pmackle/EE-Emerge-2020-FourFace/docs/Images/A.png

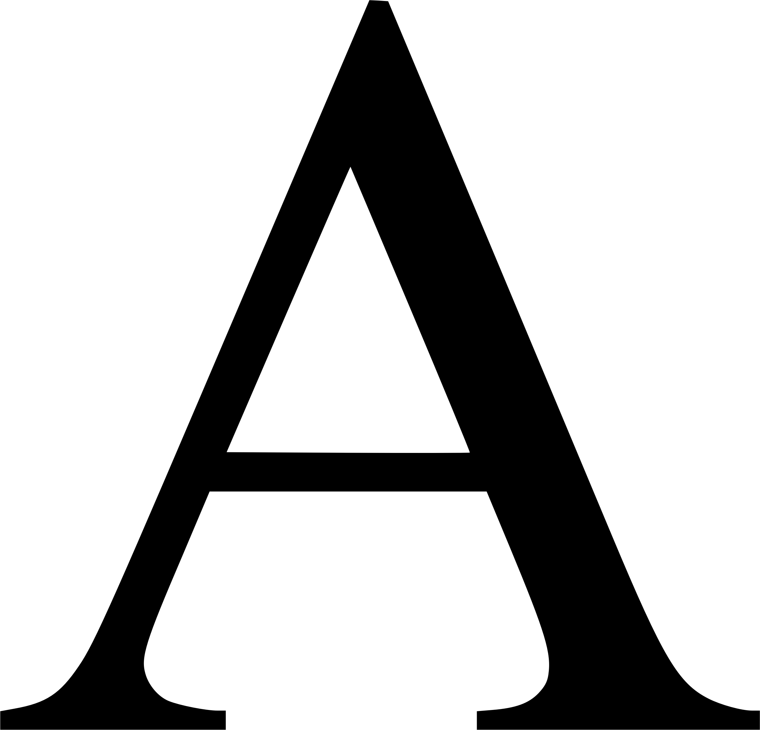
docs/Images/A.png
