pmackle/EE-Emerge-2020-FourFace/Documentation/Photos/big.png

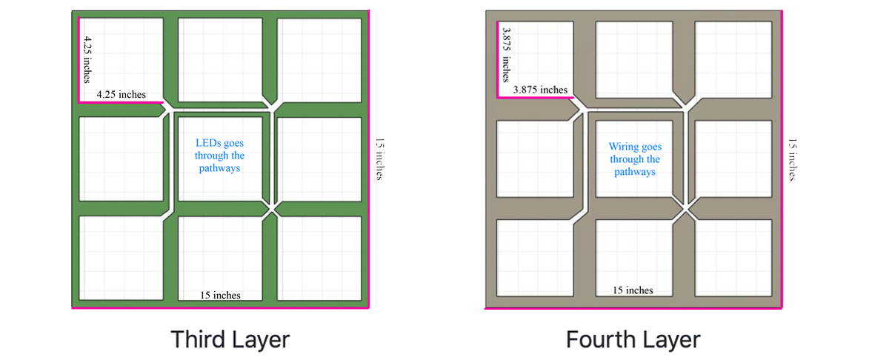
Documentation/Photos/big.png
