pmackle/EE-Emerge-2020-FourFace/Documentation/Photos/ECExpo_Adventures.jpg

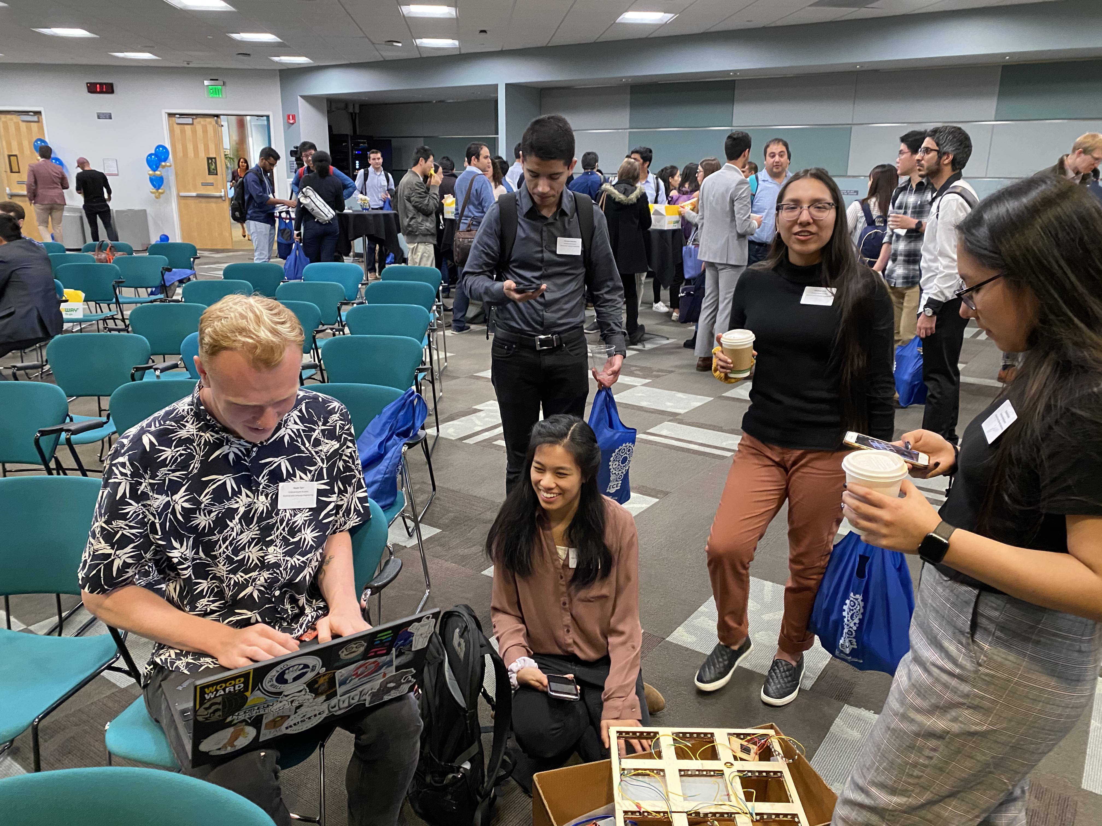
Documentation/Photos/ECExpo_Adventures.jpg
