pmackle/EE-Emerge-2020-FourFace/Documentation/Photos/First_Square_Prototype.jpg

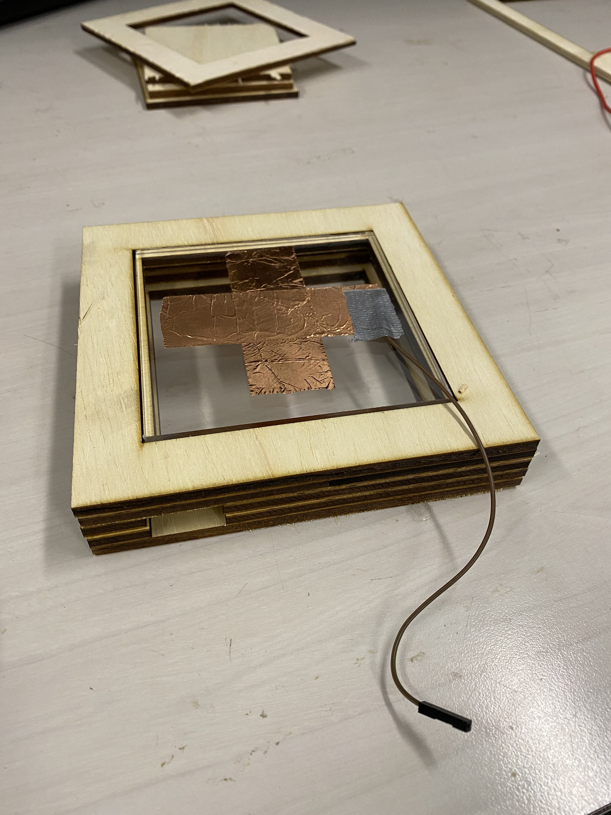
Documentation/Photos/First_Square_Prototype.jpg
