pmackle/EE-Emerge-2020-FourFace/Documentation/Photos/firstandsecond.png

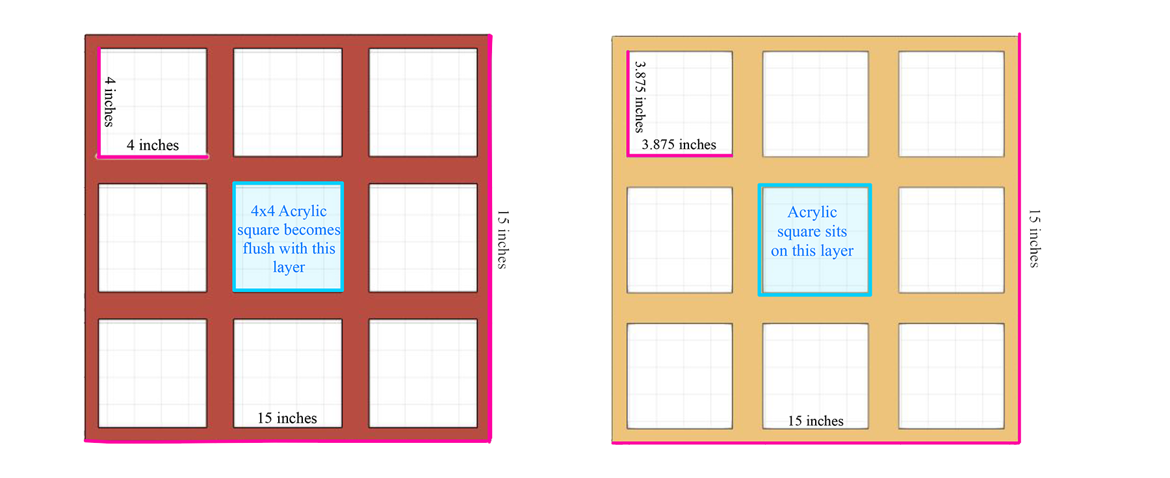
Documentation/Photos/firstandsecond.png
