pmackle/EE-Emerge-2020-FourFace/Documentation/Photos/Laser_Cutting_First_Square_Prototype.jpg

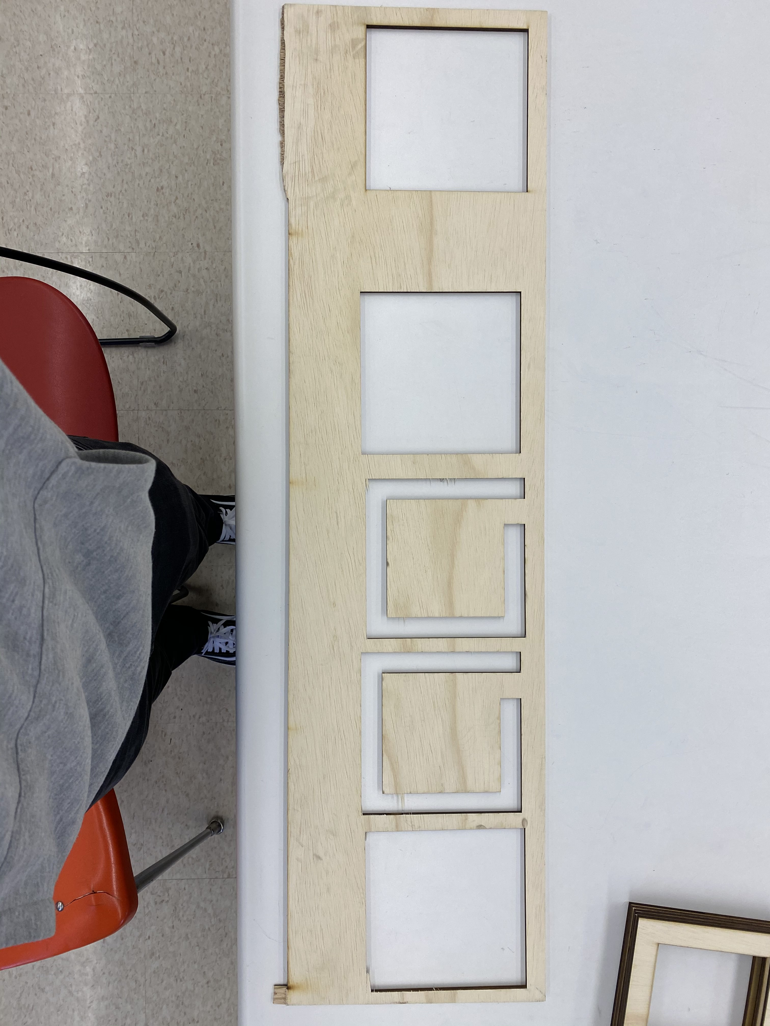
Documentation/Photos/Laser_Cutting_First_Square_Prototype.jpg
