pmackle/EE-Emerge-2020-FourFace/Documentation/Photos/michelle.png

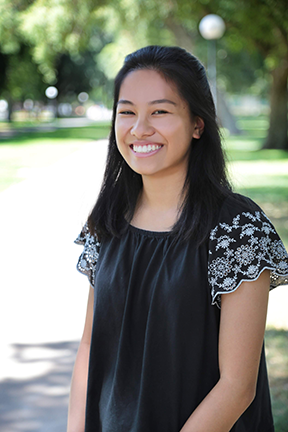
Documentation/Photos/michelle.png
