pmackle/EE-Emerge-2020-FourFace/Documentation/Photos/not.png

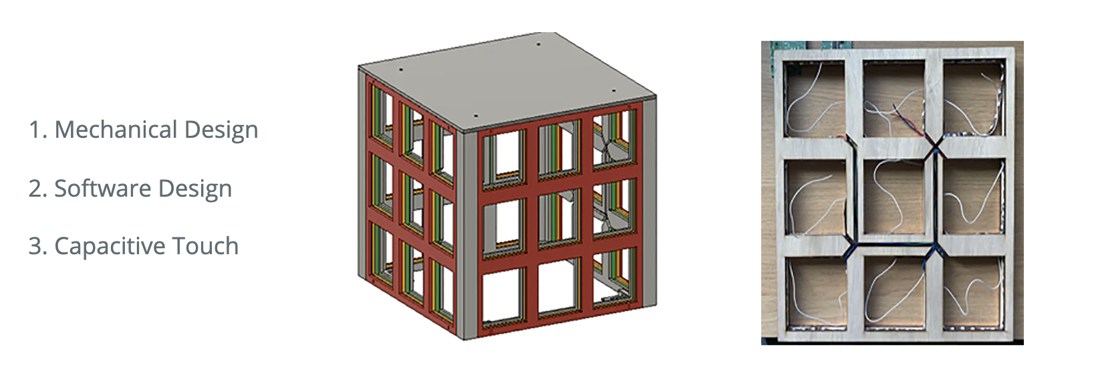
Documentation/Photos/not.png
