pmackle/EE-Emerge-2020-FourFace/Documentation/Photos/projectpage.png

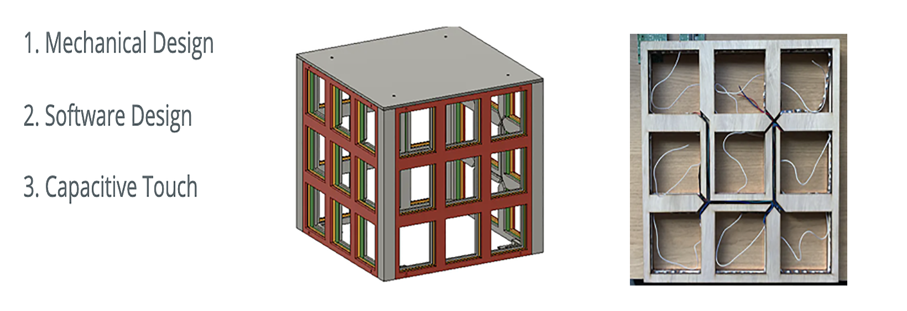
Documentation/Photos/projectpage.png
