pmackle/EE-Emerge-2020-FourFace/Documentation/Photos/Screen Shot 2020-05-14 at 4.56.53 PM.png

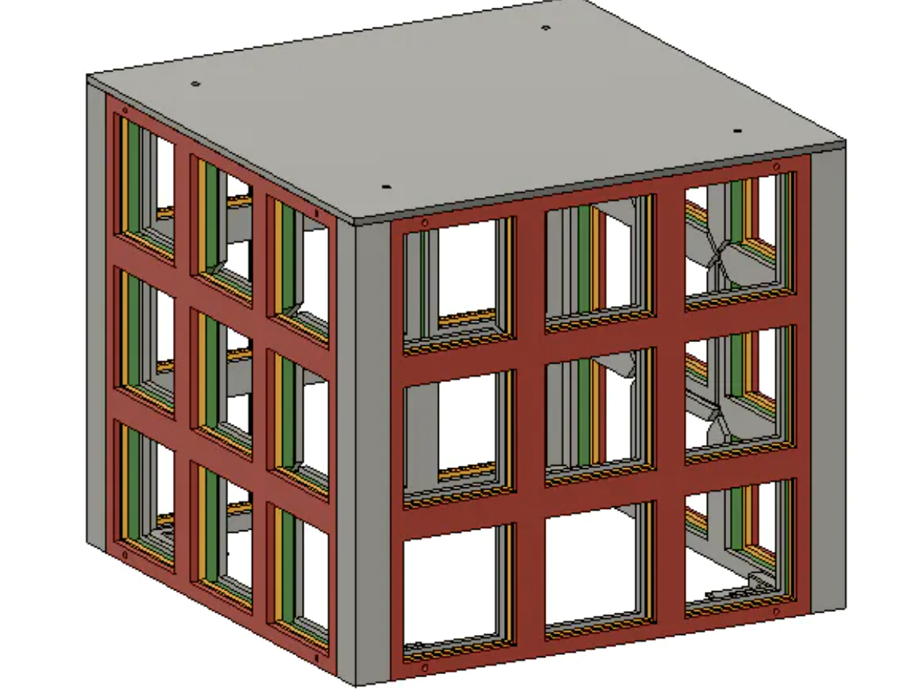
Documentation/Photos/Screen Shot 2020-05-14 at 4.56.53 PM.png
