pmackle/EE-Emerge-2020-FourFace/Documentation/Photos/team2.png

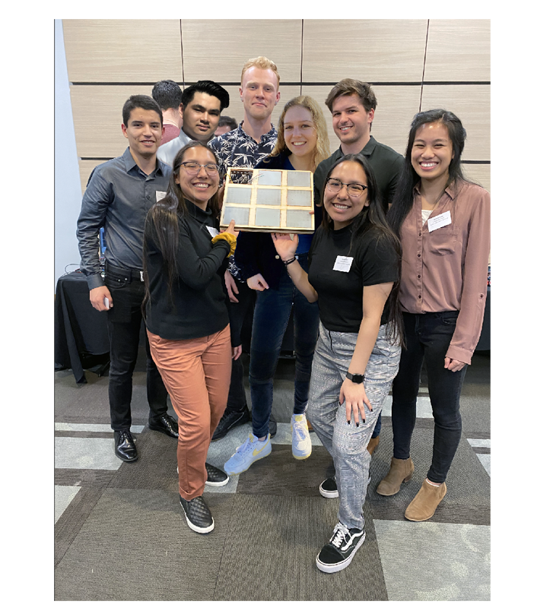
Documentation/Photos/team2.png
