pmackle/EE-Emerge-2020-FourFace/Documentation/Photos/team3.png

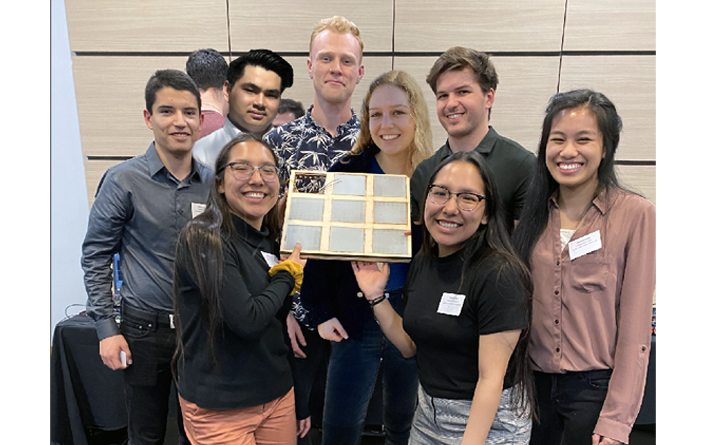
Documentation/Photos/team3.png
