pmackle/EE-Emerge-2020-FourFace/Documentation/Photos/team copy.png

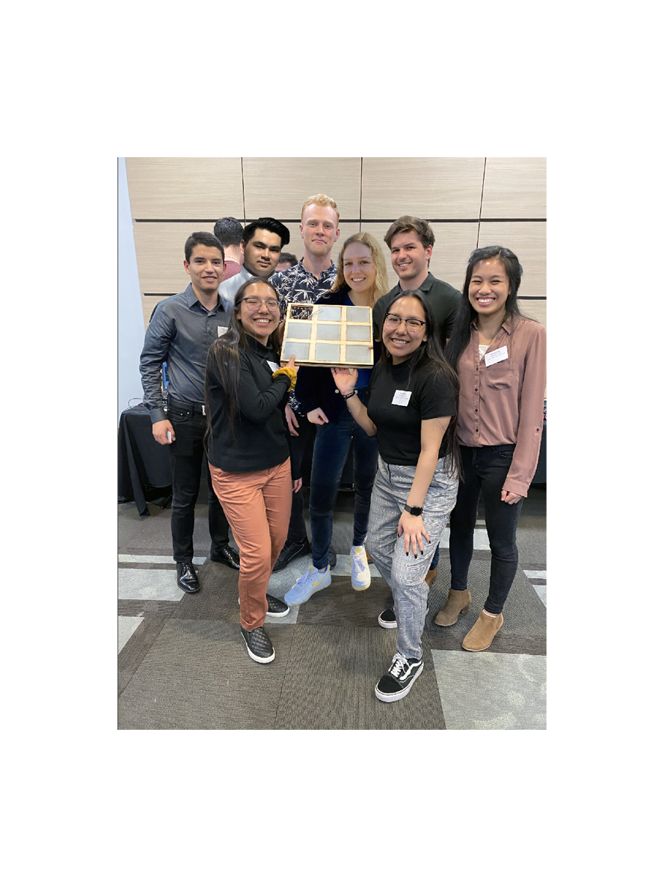
Documentation/Photos/team copy.png
