pmackle/EE-Emerge-2020-FourFace/Documentation/Photos/team.png

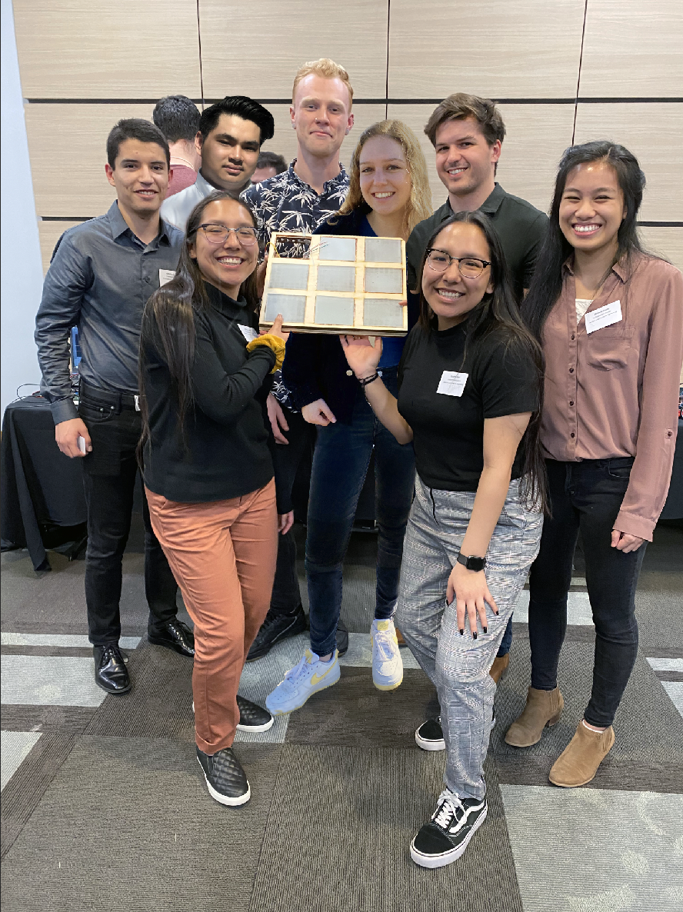
Documentation/Photos/team.png
