pmackle/EE-Emerge-2020-FourFace/Documentation/Photos/vanessa2.png

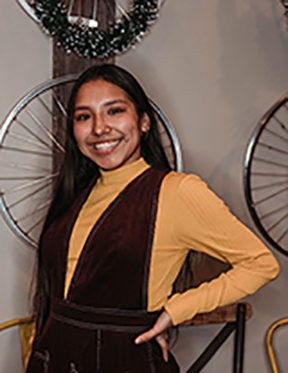
Documentation/Photos/vanessa2.png
