pmackle/EE-Emerge-2020-FourFace/Image from iOS (1).jpg

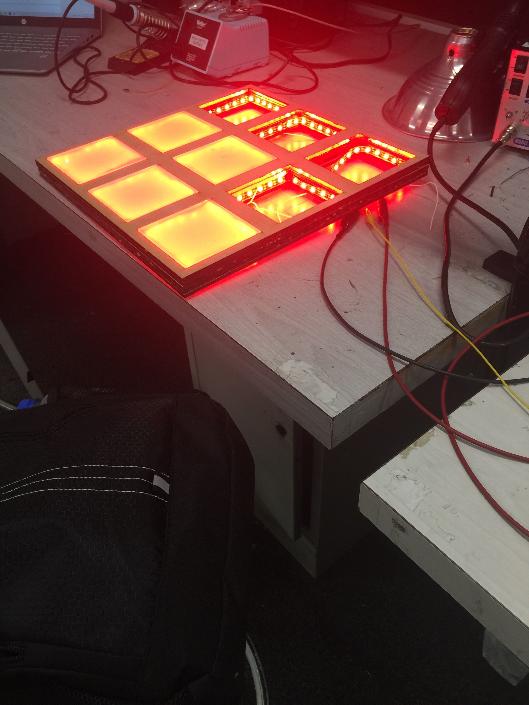
Image from iOS (1).jpg
