pmackle/EE-Emerge-2020-FourFace/Image from iOS (2).jpg

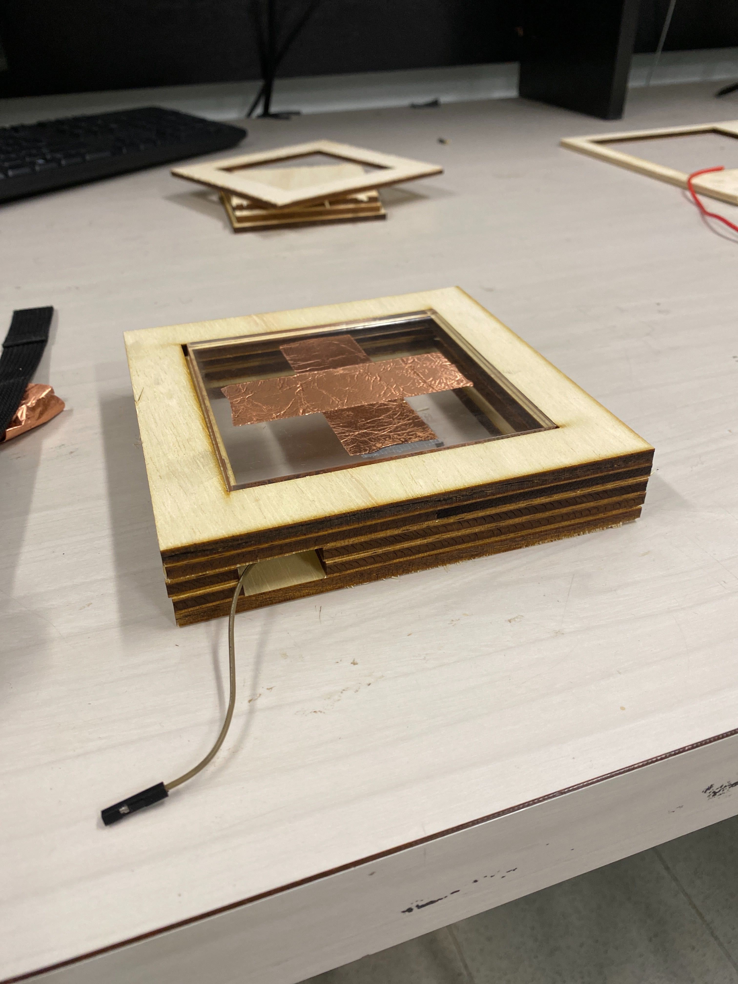
Image from iOS (2).jpg
