pmackle/EE-Emerge-2020-FourFace/Image from iOS (3).jpg

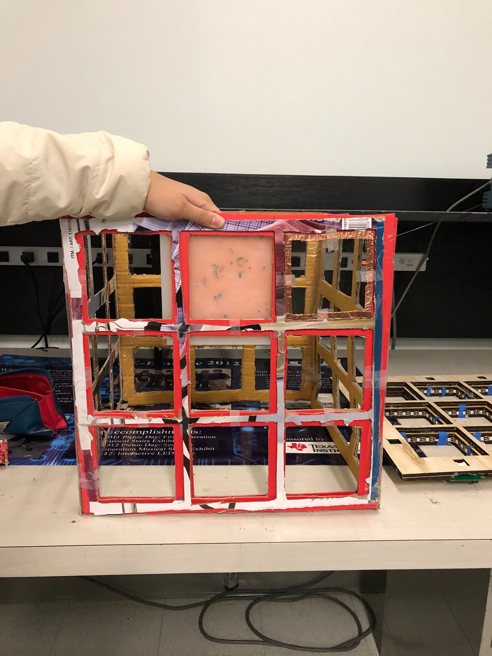
Image from iOS (3).jpg
