pmackle/EE-Emerge-2020-FourFace/Image from iOS.jpg

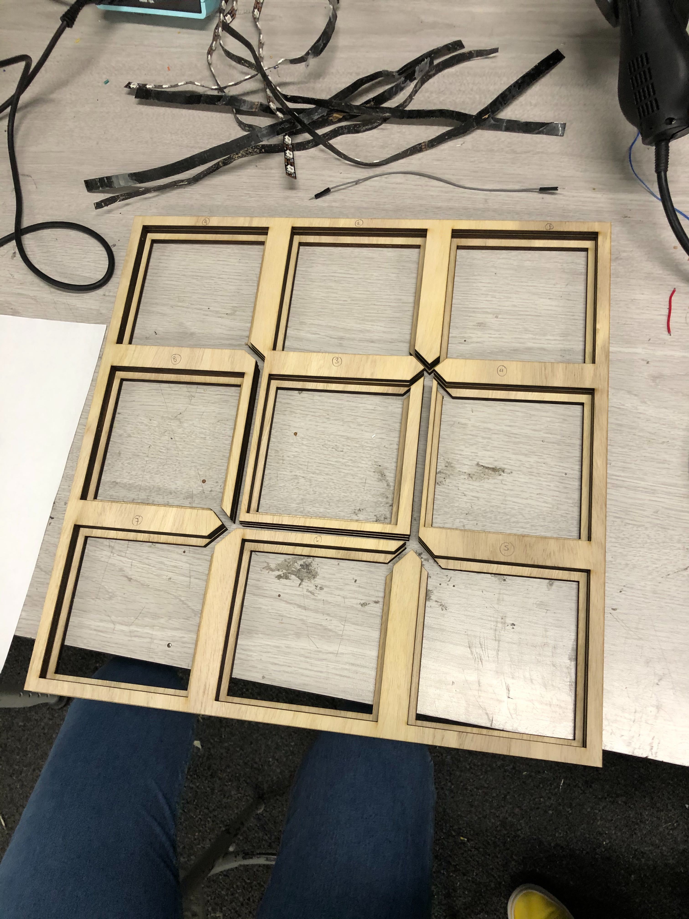
Image from iOS.jpg
