pmackle/EE-Emerge-2020-FourFace/IMG_2035.jpg

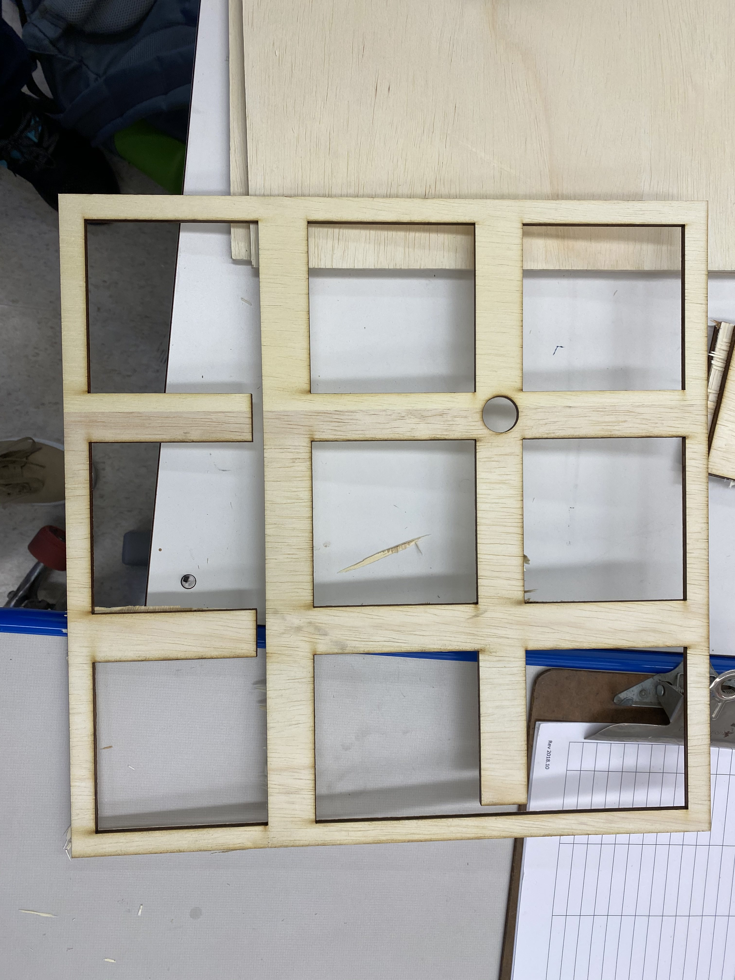
IMG_2035.jpg
