pmackle/EE-Emerge-2020-FourFace/IMG_3783.JPG

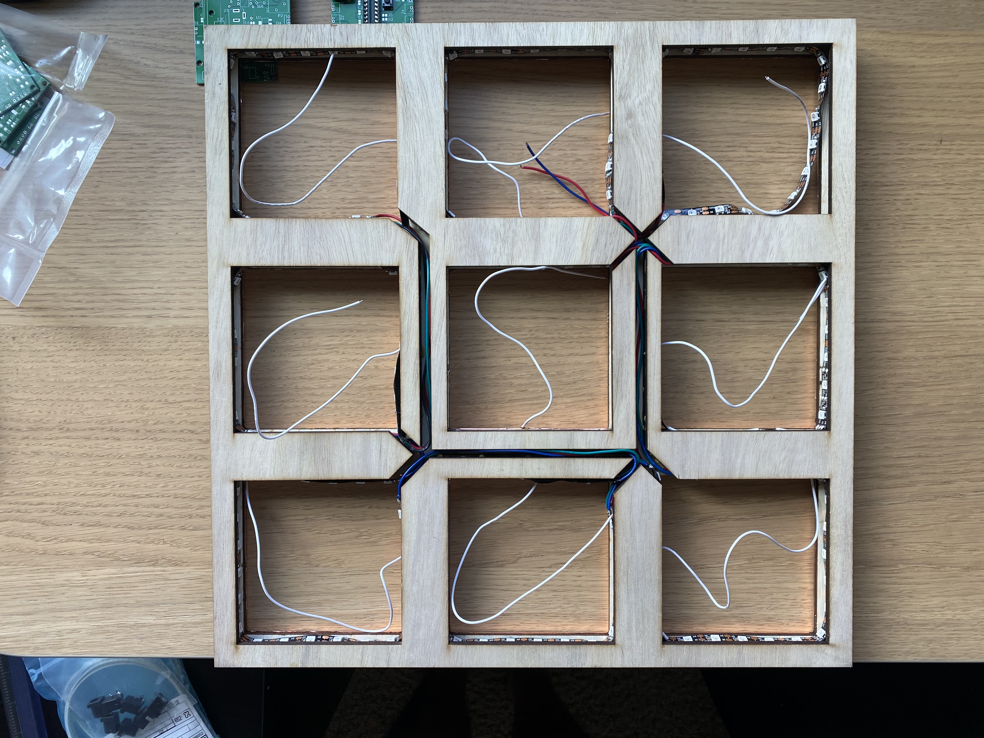
IMG_3783.JPG
