pmackle/EE-Emerge-2020-FourFace/Mechanical/Components/FourFaceLayers Front.PNG

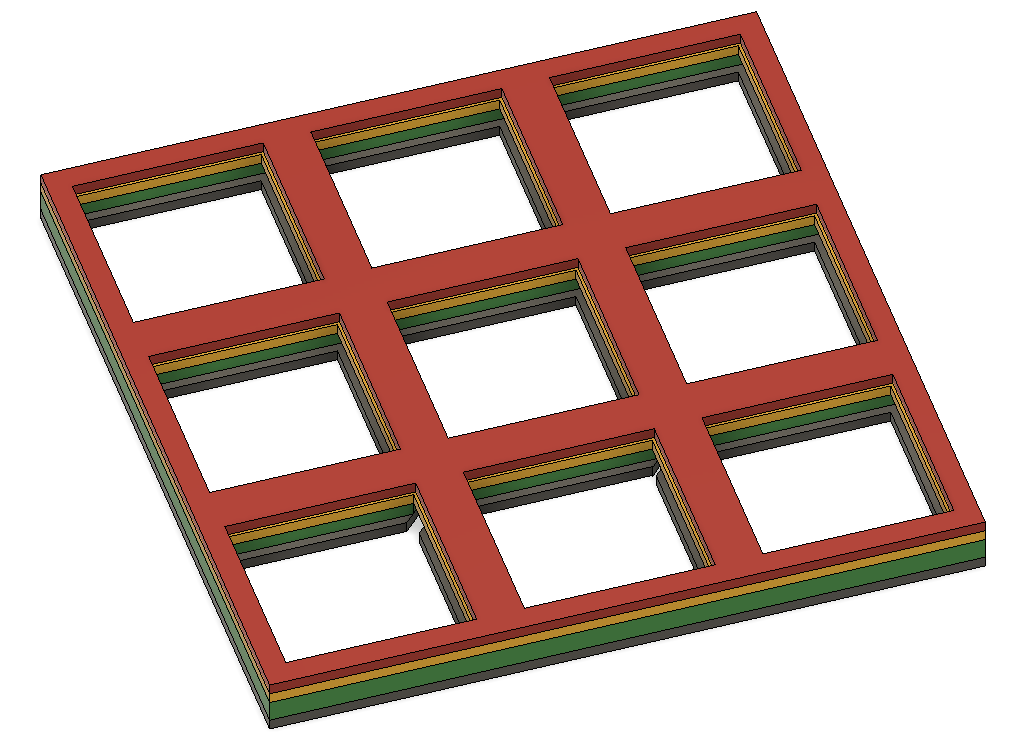
Mechanical/Components/FourFaceLayers Front.PNG
