pmackle/EE-Emerge-2020-FourFace/Documentation/Photos/Assembling_First_FrameP2.jpg

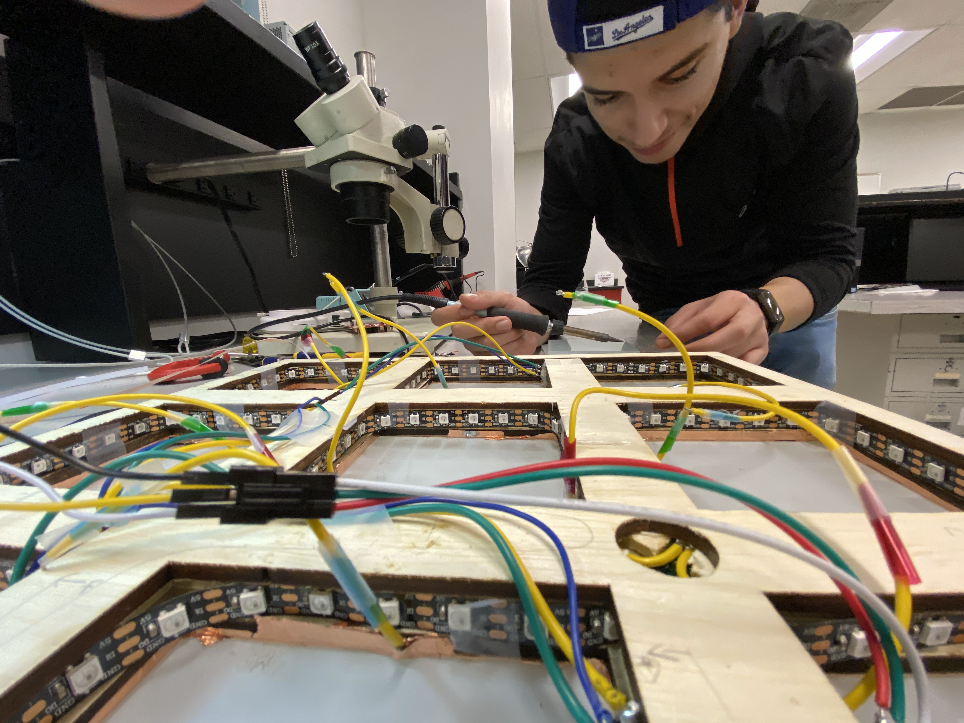
Documentation/Photos/Assembling_First_FrameP2.jpg
