pmackle/EE-Emerge-2020-FourFace/Documentation/Photos/First_Frame_Assembled.jpg

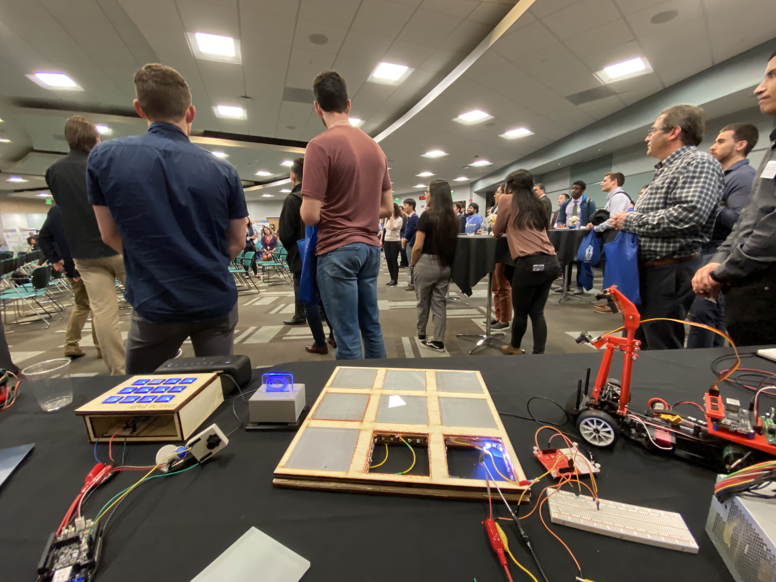
Documentation/Photos/First_Frame_Assembled.jpg
