pmackle/EE-Emerge-2020-FourFace/Documentation/Photos/Frame_Layers_Assembled.jpg

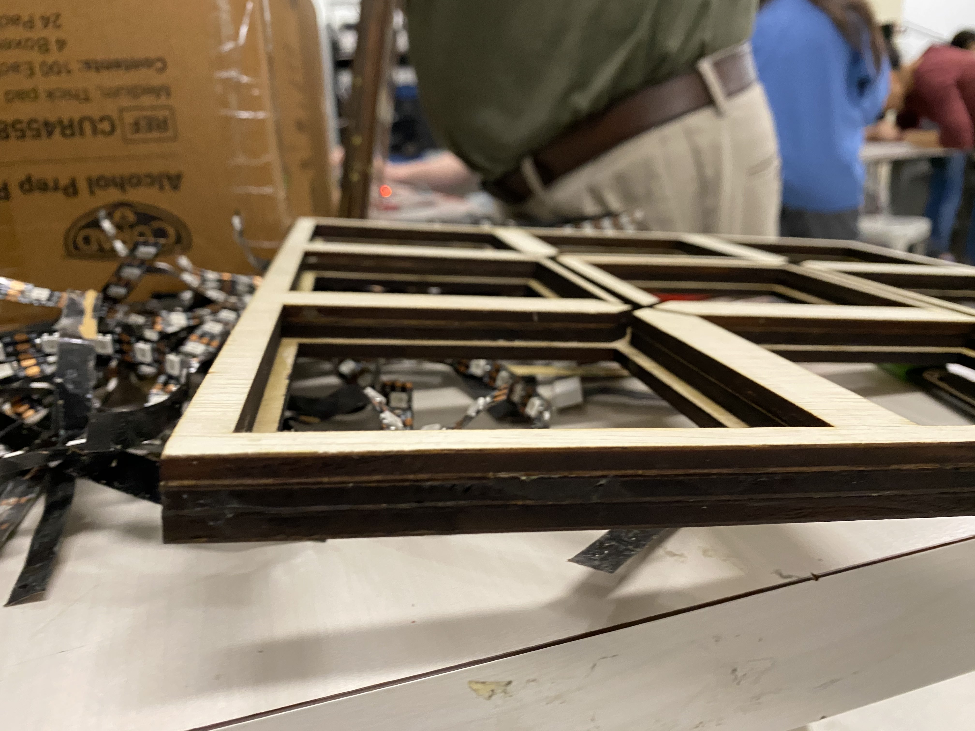
Documentation/Photos/Frame_Layers_Assembled.jpg
