pmackle/EE-Emerge-2020-FourFace/Mechanical/Wiring.png

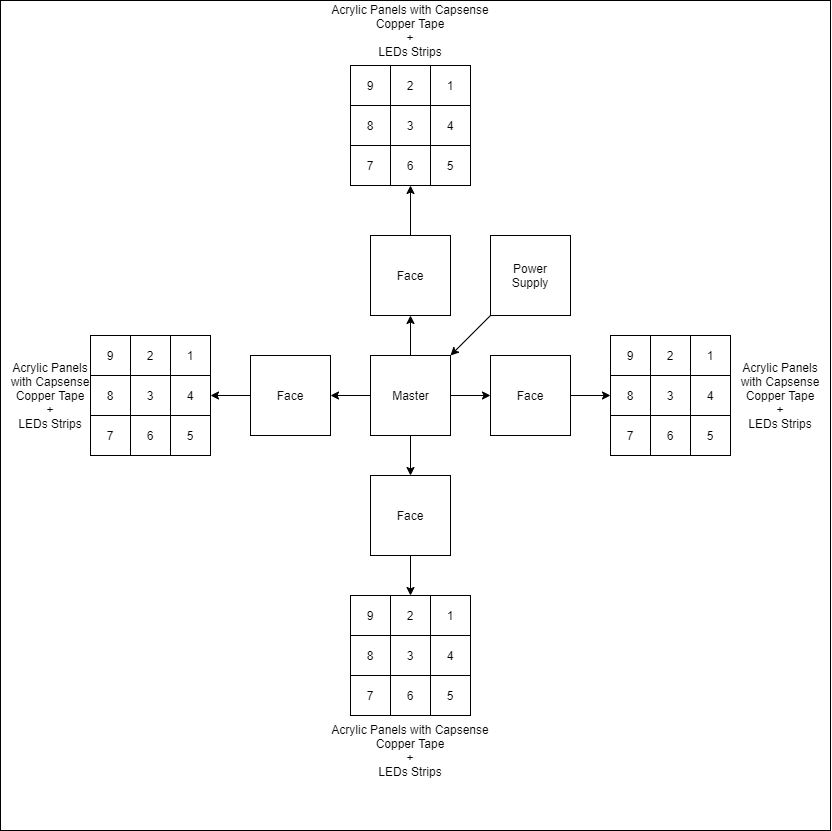
Mechanical/Wiring.png
