pmackle/EE-Emerge-2020-FourFace/Documentation/Photos/Testing_CapSense.jpg

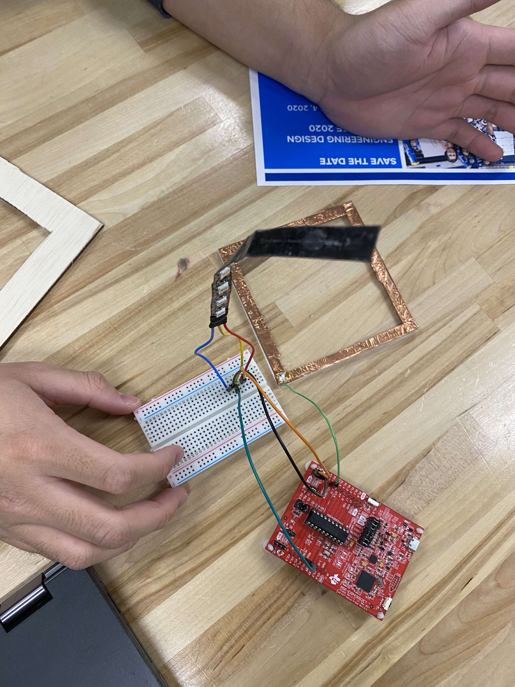
Documentation/Photos/Testing_CapSense.jpg
