pmackle/EE-Emerge-2020-FourFace/IMG_3365.jpg

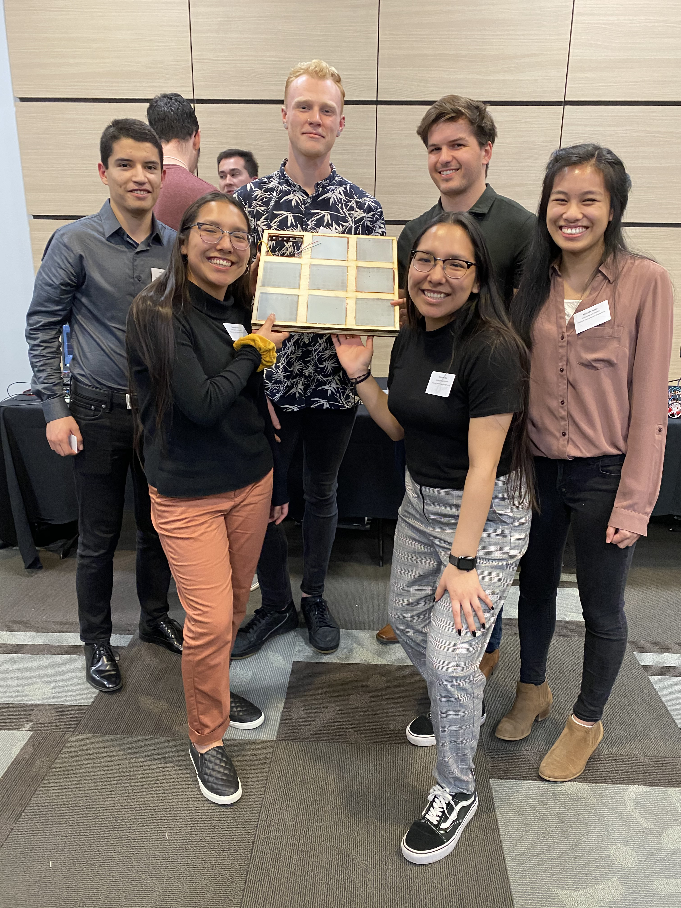
IMG_3365.jpg
