pmackle/EE-Emerge-2020-FourFace/IMG_3782.JPG

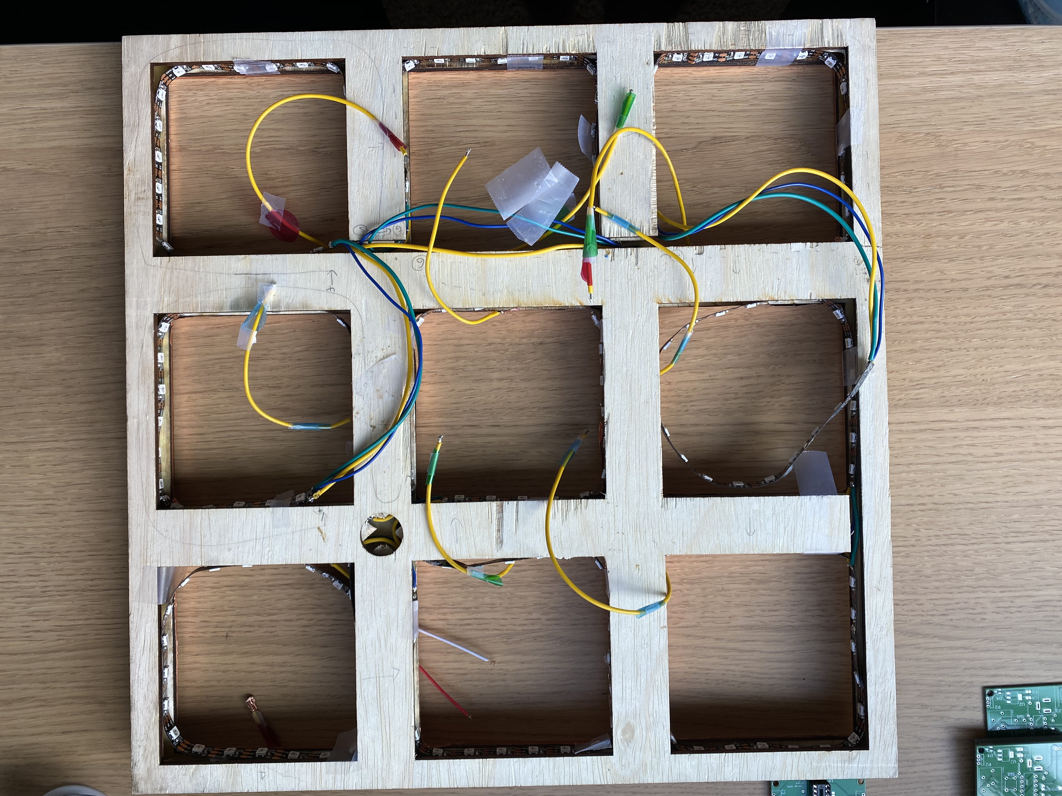
IMG_3782.JPG
